in-tech/SmartSign/docs/images/frame_led_off.png

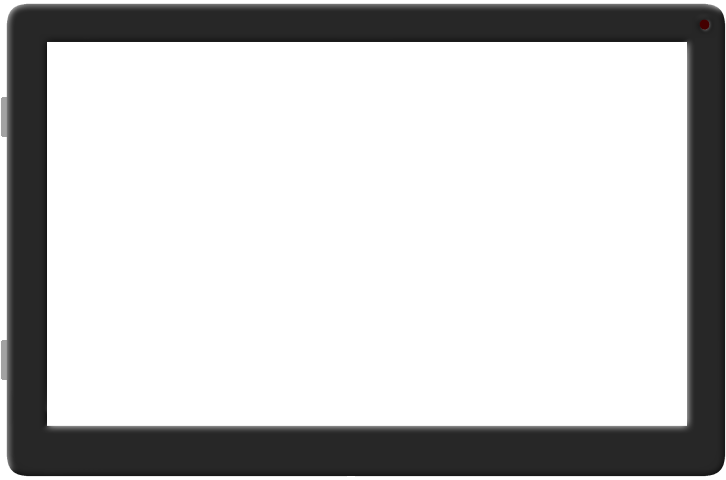
docs/images/frame_led_off.png
